KenwoodFox/FSK-Project/Writeup/Figures/PXL_20260402_165301376.jpg

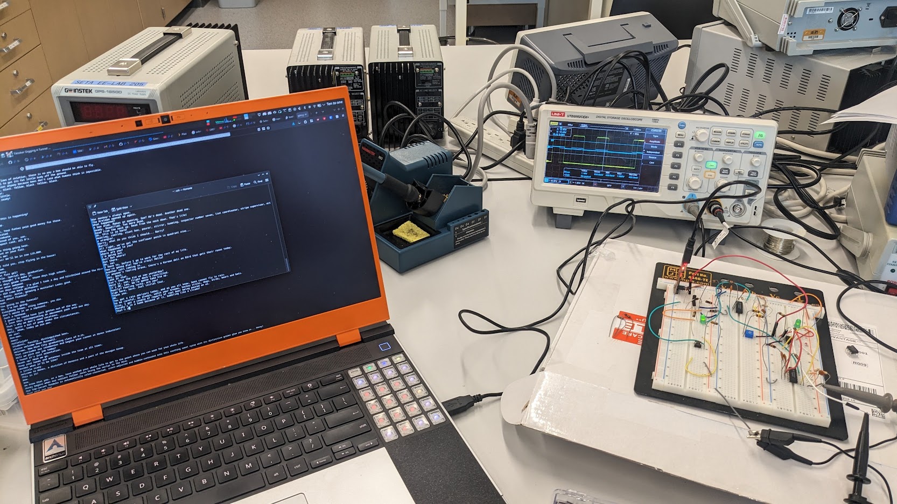
Writeup/Figures/PXL_20260402_165301376.jpg
