KenwoodFox/FSK-Project/Writeup/Figures/PXL_20260414_150821640.jpg

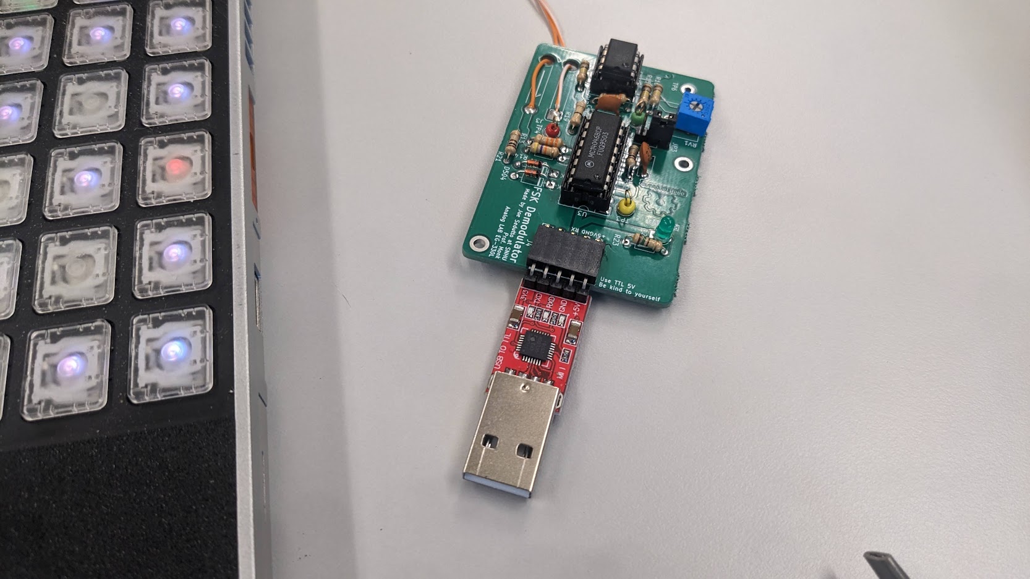
Writeup/Figures/PXL_20260414_150821640.jpg
