KenwoodFox/FSK-Project/Writeup/Figures/PXL_20260418_175138862.jpg

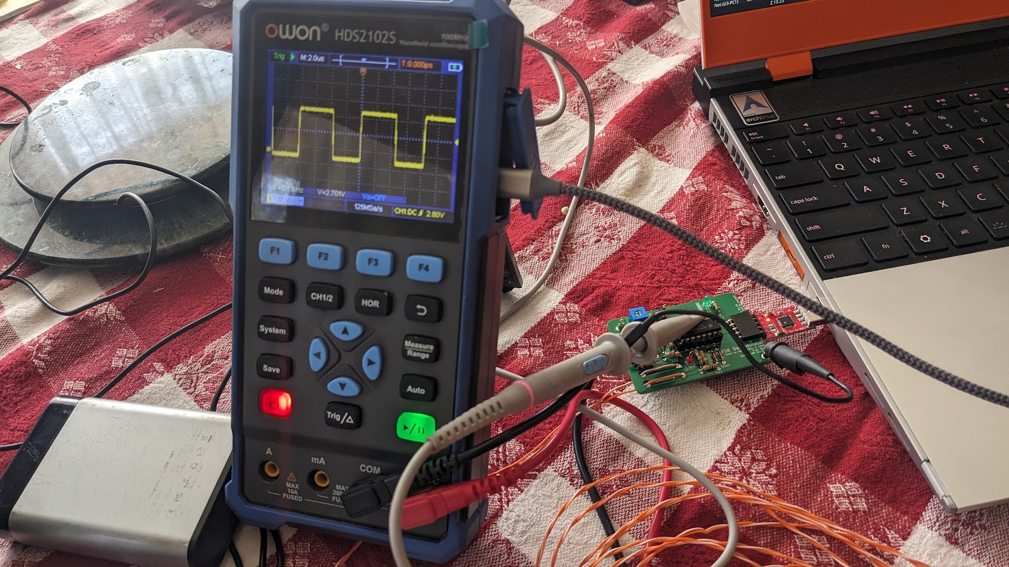
Writeup/Figures/PXL_20260418_175138862.jpg
